stevenchadburrow/MicroTetra887/assembly.asm

field	 	EQU 0x0020

vert		EQU 0x0050
scale		EQU 0x0051

pixel0		EQU 0x0070
pixel1		EQU 0x0071
pixel2		EQU 0x0072
pixel3		EQU 0x0073
pixel4		EQU 0x0074
pixel5		EQU 0x0075
pixel6		EQU 0x0076
pixel7		EQU 0x0077
pixel8		EQU 0x0078
pixel9		EQU 0x0079
pixelA		EQU 0x007A
pixelB		EQU 0x007B


; assumes you ran 'CLRW' and 'CLFW 0x03' already

PSECT		my_code,abs,ovrld,global,class=CODE,delta=2
ORG 0x0800
GLOBAL _table_line
_table_line:
	ADDWF 0x02
	GOTO line0
	GOTO line1
	GOTO line2
	GOTO line3
	GOTO line0
	GOTO line1
	GOTO line2
	GOTO line3
	GOTO line4
	GOTO line5
	GOTO line0
	GOTO line1
	GOTO line2
	GOTO line3
	GOTO line4
	GOTO line5
	GOTO line0
	GOTO line1
	GOTO line2
	GOTO line3
	GOTO line4
	GOTO line5	

GLOBAL _table_bank
_table_bank:
	ADDWF 0x02
	RETLW 0x00
	RETLW 0x00
	RETLW 0x00
	RETLW 0x00
	RETLW 0x20
	RETLW 0x20
	RETLW 0x20
	RETLW 0x20
	RETLW 0x20
	RETLW 0x20
	RETLW 0x40
	RETLW 0x40
	RETLW 0x40
	RETLW 0x40
	RETLW 0x40
	RETLW 0x40
	RETLW 0x60
	RETLW 0x60
	RETLW 0x60
	RETLW 0x60
	RETLW 0x60
	RETLW 0x60

GLOBAL _scanlines
_scanlines:	
	; set up variables
	CLRF vert
	MOVLW 0x10 ; 16 pixels wide
	MOVWF scale

wait0:
	; nop padding
	NOP
	NOP
	NOP
	NOP
	NOP
	NOP
	NOP
	NOP
	NOP
	NOP
	NOP
	NOP
	NOP
	NOP
	NOP
	NOP
	NOP
	NOP
	NOP
	NOP
	NOP
	NOP
	NOP
	NOP
	NOP
	NOP
	NOP
	NOP
	NOP
	NOP
	NOP
	NOP
	NOP
	NOP
	NOP
	NOP
	NOP
	NOP
	NOP
	NOP
	NOP
	NOP
	NOP
	NOP
	NOP
	NOP
	NOP
	NOP
	NOP
	NOP
	NOP
	NOP
	NOP
	NOP
	NOP
	NOP
	NOP
	NOP
	NOP
	NOP
	NOP
	NOP
	NOP

loop:
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
	BTFSS 0x03,2
	GOTO wait2
	RETURN

wait1:
	; nop padding
	NOP
	NOP
	NOP
	NOP
	NOP
	NOP
	NOP
	NOP

wait2:
	; nop padding
	NOP
	NOP
	NOP
	NOP
	NOP
	NOP
	NOP
	NOP
	NOP
	NOP
	NOP
	NOP
	NOP
	NOP
	NOP
	NOP
	NOP
	NOP
	NOP
	NOP
	NOP
	NOP
	NOP
	NOP
	; add more here

	GOTO loop
